FloppyO1/Floppy_Boards/Floppy Board/Floppy Board 2/STM32G030F6P6  v2.0/pannel/IMMAGINE.png

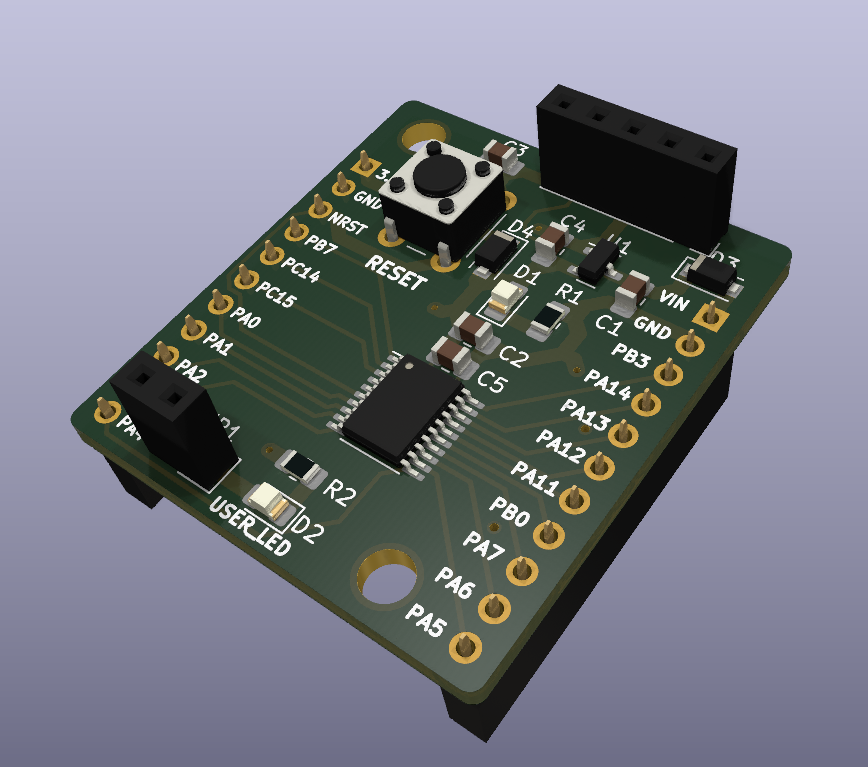
Floppy Board/Floppy Board 2/STM32G030F6P6 v2.0/pannel/IMMAGINE.png
